Picatout/stm8_terminal/kiCAD/stm8_terminal/stm8_terminal.kicad_sch

## KiCad design kiCAD/stm8_terminal/stm8_terminal.kicad_sch (2024-02-14, an earlier design)

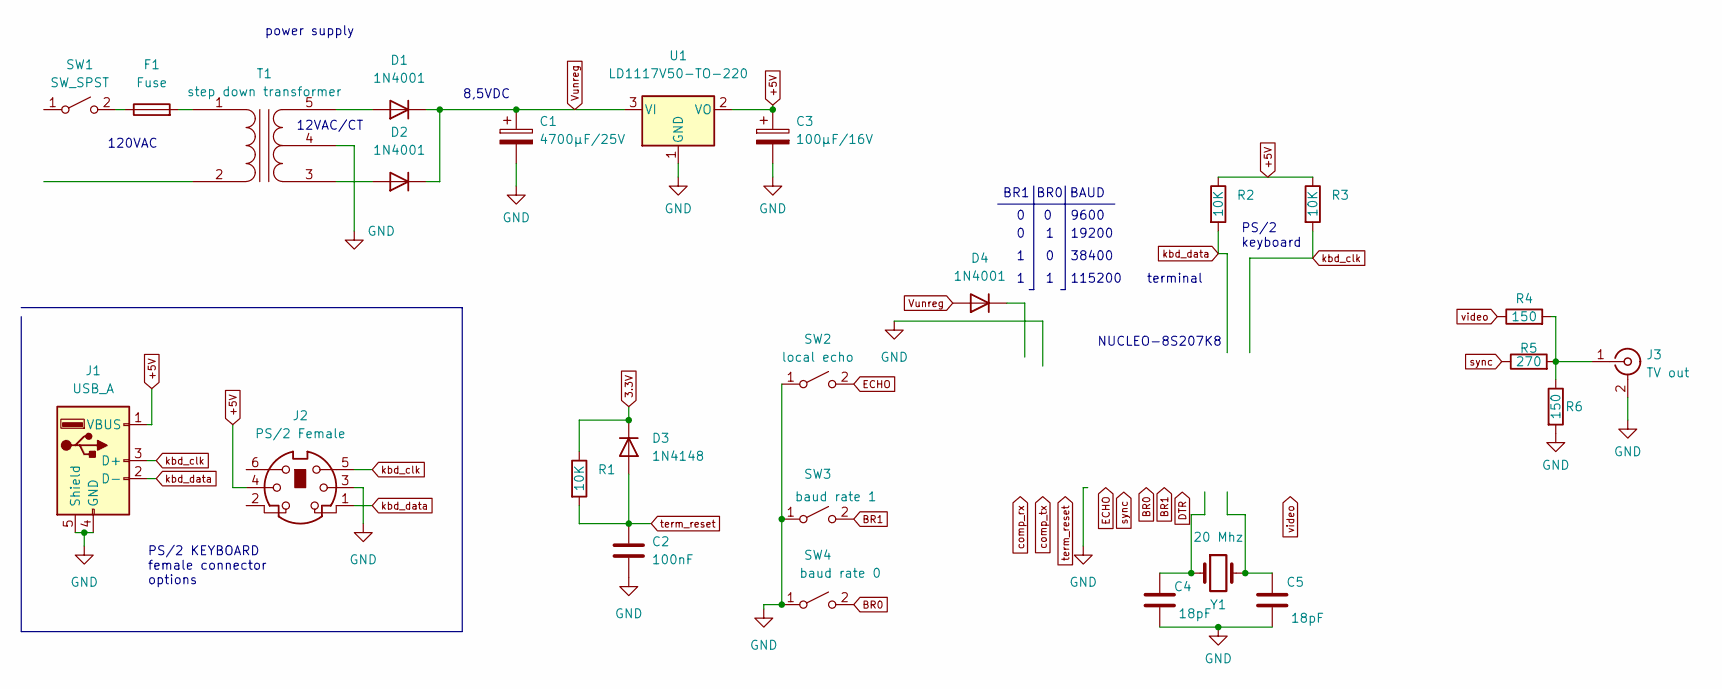
[picture p4: schematic stm8_terminal.kicad_sch]

Parts:
C1: 4700µF/25V
C2: 100nF
C3: 100µF/16V
C4, C5: 18pF
D1, D2, D4: 1N4001; D_DO-41_SOD81_P10.16mm_Horizontal
D3: 1N4148; D_DO-35_SOD27_P7.62mm_Horizontal
F1: Fuse
J1: USB_A
J2: PS/2 Female
J3: TV out
R1, R2, R3: 10K
R4, R6: 150
R5: 270
SW1: SW_SPST
SW2: local echo
SW3: baud rate 1
SW4: baud rate 0
T1: step down transformer
U1: LD1117V50-TO-220; SOT-223-3_TabPin2
Y1: 20 Mhz

Connections:
3.3V: D3.1 (K), R1.1
+5V: C3.1, J1.1 (VBUS), J2.4, R2.1, R3.1, U1.2 (VO)
BR0: SW4.2 (B)
BR1: SW3.2 (B)
ECHO: SW2.2 (B)
GND: C1.2, C2.2, C3.2, C4.2, C5.2, J1.4 (GND), J1.5 (Shield), J2.3, J3.2 (Ext), R6.2, SW2.1 (A), SW3.1 (A), SW4.1 (A), T1.4 (SC), U1.1 (GND)
unnamed: C4.1, Y1.1
unnamed: C5.1, Y1.2
unnamed: D1.2 (A), T1.5 (SB)
unnamed: D2.2 (A), T1.3 (SA)
unnamed: F1.1, SW1.2 (B)
unnamed: F1.2, T1.1 (AA)
unnamed: J3.1 (In), R4.2, R5.2, R6.1
Vunreg: C1.1, D1.1 (K), D2.1 (K), D4.2 (A), U1.3 (VI)
kbd_clk: J1.3 (D+), J2.5, R3.2
kbd_data: J1.2 (D-), J2.1, R2.2
sync: R5.1
term_reset: C2.1, D3.2 (A), R1.2
video: R4.1

Notes on the sheet:
1 0
1 1
38400
120VAC
BR1 BR0 BAUD
PS/2 keyboard
terminal
19200
9600
NUCLEO-8S207K8
power supply
12VAC/CT
0 1
8,5VDC
PS/2 KEYBOARD female connector options
115200
